ColMWillis/MissionComHub/images/R0.5_preview.png

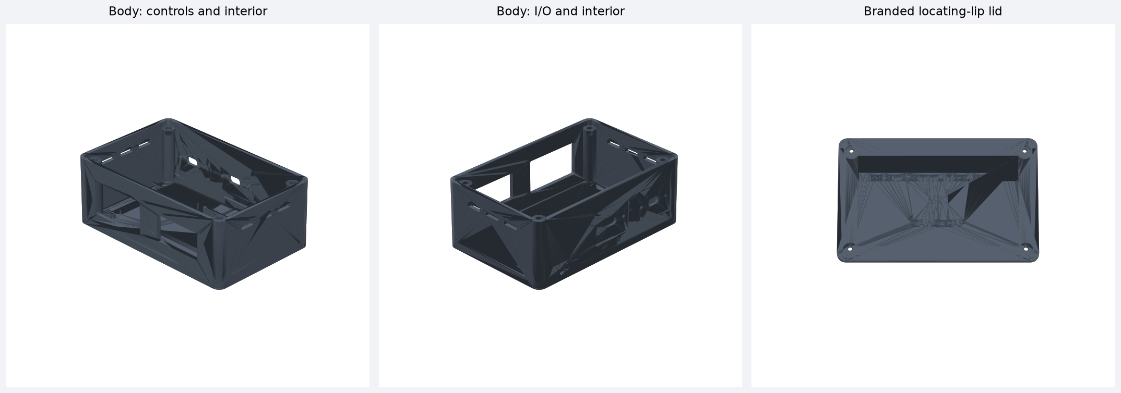
images/R0.5_preview.png
