ColMWillis/MissionComHub/CAD/STEP/R0.12/MCH-MkI_dual_USB-PD_card_carrier_R0.12.step

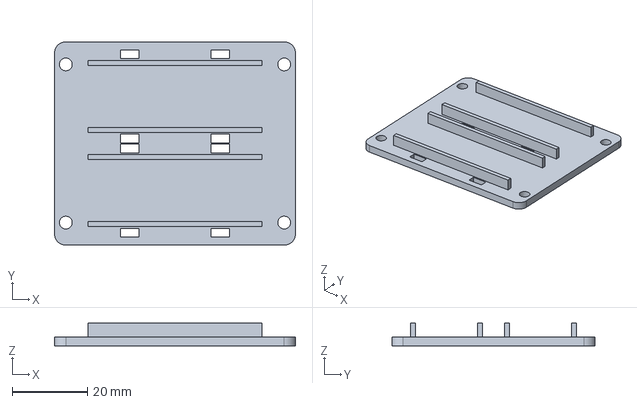
[picture p17: CAD file, 2026-07-24]
CAD/STEP/R0.12/MCH-MkI_dual_USB-PD_card_carrier_R0.12.step
64.0 x 54.0 x 6.00 mm
