ColMWillis/MissionComHub/CAD/STEP/R0.6/MCH-MkI_body_R0.6.step

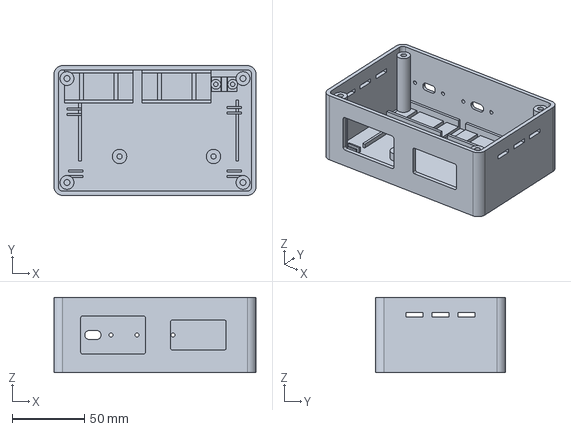
[picture p18: CAD file, 2026-07-22]
CAD/STEP/R0.6/MCH-MkI_body_R0.6.step
140.0 x 90.0 x 52.0 mm
