ColMWillis/MissionComHub/CAD/STEP/R0.9/MCH-MkI_body_R0.9.step

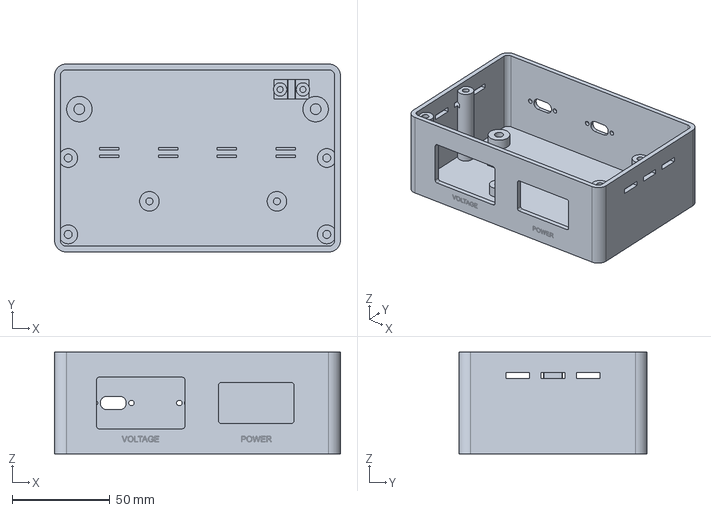
[picture p19: CAD file, 2026-07-23]
CAD/STEP/R0.9/MCH-MkI_body_R0.9.step
146.0 x 96.0 x 52.0 mm
