ColMWillis/MissionComHub/CAD/STEP/R0.11/MCH-MkI_dual_USB-PD_card_carrier_R0.11.step

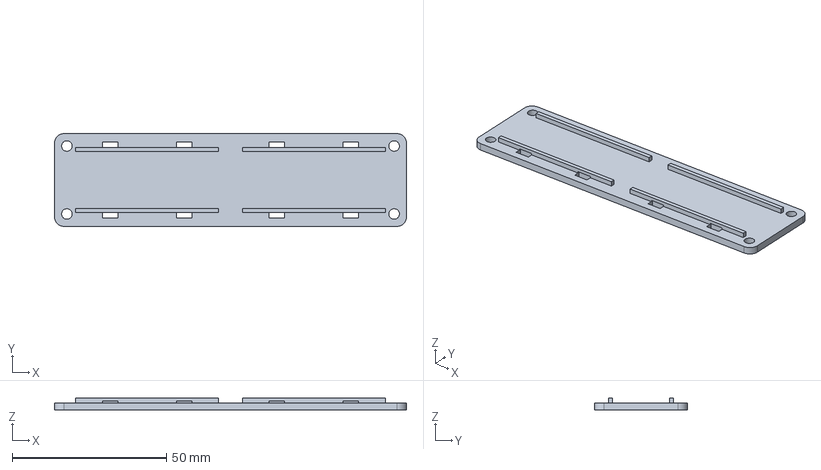
[picture p20: CAD file, 2026-07-23]
CAD/STEP/R0.11/MCH-MkI_dual_USB-PD_card_carrier_R0.11.step
114.0 x 30.0 x 4.00 mm
