ColMWillis/MissionComHub/CAD/STEP/R0.9/MCH-MkI_lid_R0.9.step

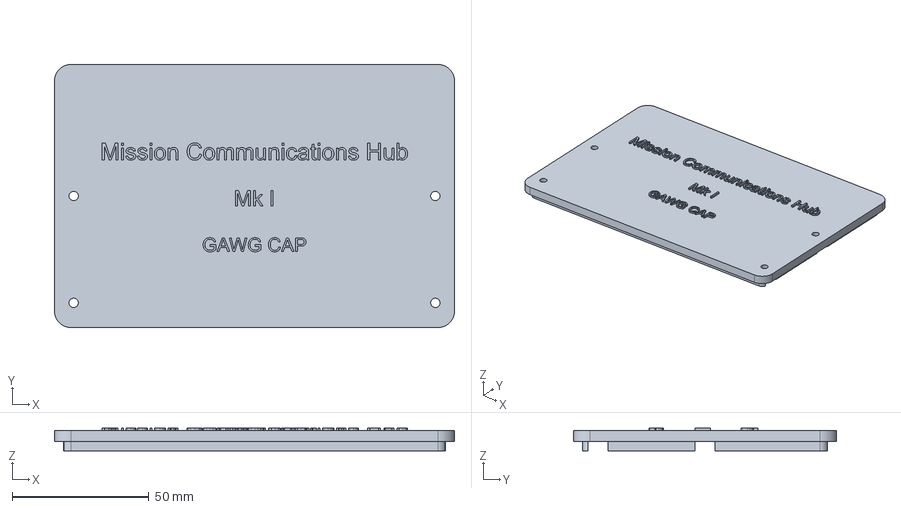
[picture p21: CAD file, 2026-07-23]
CAD/STEP/R0.9/MCH-MkI_lid_R0.9.step
146.0 x 96.0 x 8.30 mm
