ColMWillis/MissionComHub/CAD/STEP/R0.8/MCH-MkI_USB-C_panel_fit_coupon_R0.8.step

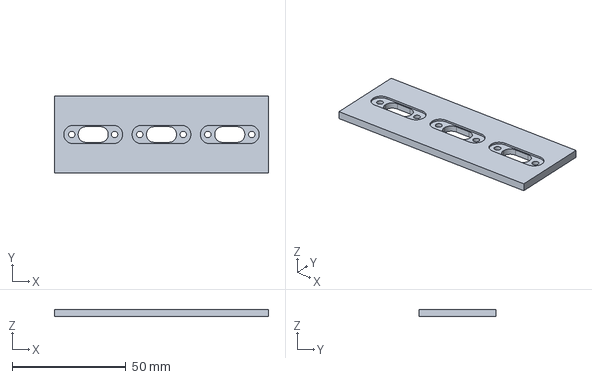
[picture p22: CAD file, 2026-07-23]
CAD/STEP/R0.8/MCH-MkI_USB-C_panel_fit_coupon_R0.8.step
94.0 x 34.0 x 3.20 mm
